nlegendree/line-following-robot/src/buzzer.c

#include "buzzer.h"

#include <wiringPi.h>

#include "gpioPins.h"

// Buzzer initialization
void initBuzzer() {
    pinMode(PIN_BUZZER, OUTPUT);
}

// Function to turn on the buzzer
void buzzerOn() {
    digitalWrite(PIN_BUZZER, HIGH);
}

// Function to turn off the buzzer
void buzzerOff() {
    digitalWrite(PIN_BUZZER, LOW);
}
